juthomas/Electronics_MDMA/Images/MDMA_Images/8th_wonder.png

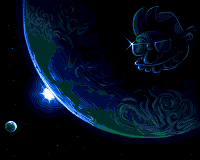
Images/MDMA_Images/8th_wonder.png
