juthomas/Electronics_MDMA/Images/MDMA_Images/background choice.png

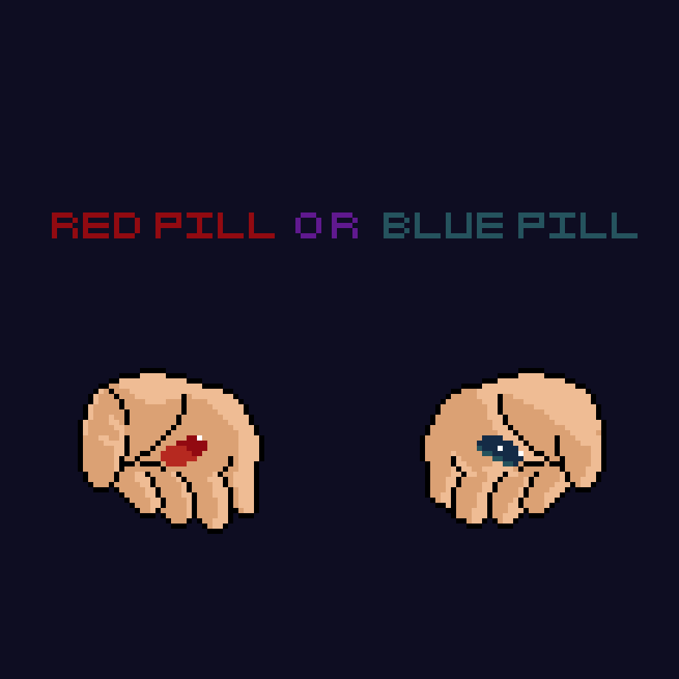
Images/MDMA_Images/background choice.png
