juthomas/Electronics_MDMA/Images/MDMA_Images/background hand.gif

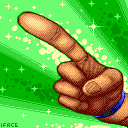
Images/MDMA_Images/background hand.gif
