juthomas/Electronics_MDMA/Images/MDMA_Images/background liar.gif

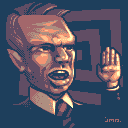
Images/MDMA_Images/background liar.gif
