juthomas/Electronics_MDMA/Images/MDMA_Images/background liar.png

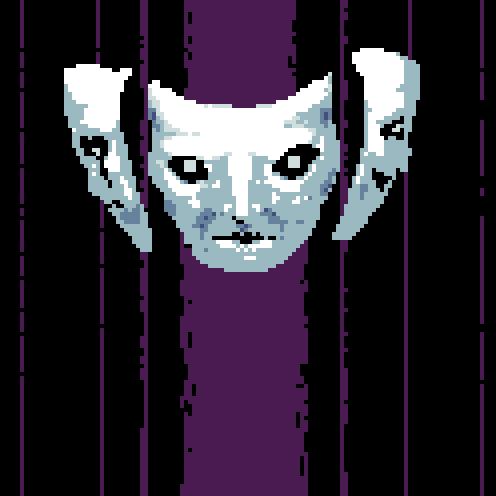
Images/MDMA_Images/background liar.png
