juthomas/Electronics_MDMA/Images/MDMA_Images/background roulette.jpeg

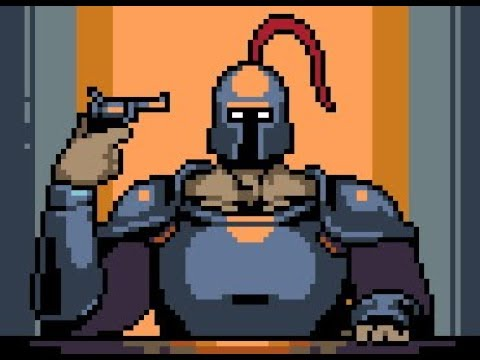
Images/MDMA_Images/background roulette.jpeg
