juthomas/Electronics_MDMA/Images/MDMA_Images/background_gunslayer.png

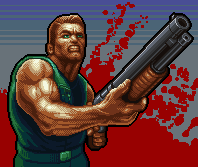
Images/MDMA_Images/background_gunslayer.png
