juthomas/Electronics_MDMA/Images/MDMA_Images/corridor.jpeg

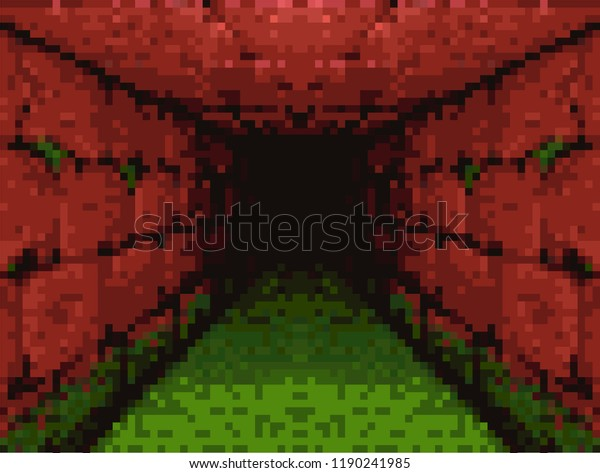
Images/MDMA_Images/corridor.jpeg
