juthomas/Electronics_MDMA/Images/MDMA_Images/Demonic.jpeg

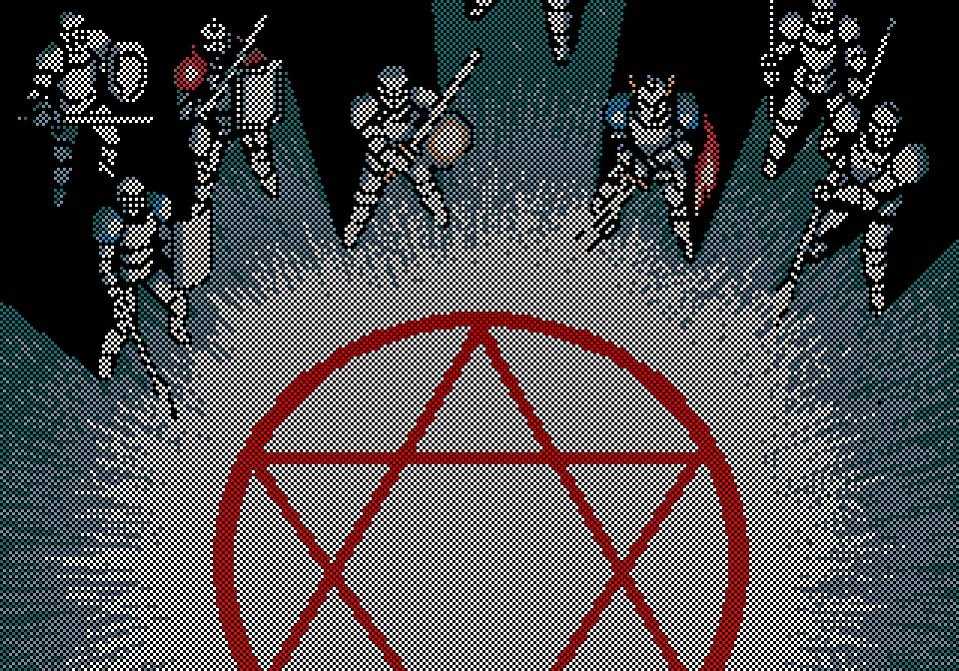
Images/MDMA_Images/Demonic.jpeg
