juthomas/Electronics_MDMA/Images/MDMA_Images/Drink.png

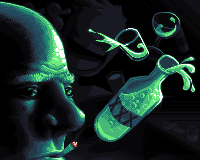
Images/MDMA_Images/Drink.png
