juthomas/Electronics_MDMA/Images/MDMA_Images/KingCrimson.png

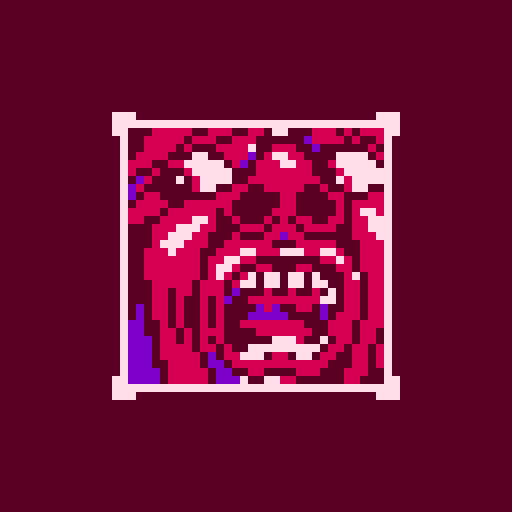
Images/MDMA_Images/KingCrimson.png
