juthomas/Electronics_MDMA/Images/MDMA_Images/time background.gif

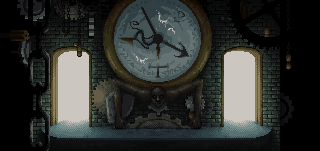
Images/MDMA_Images/time background.gif
