juthomas/Electronics_MDMA/Images/partition_megalovania.png

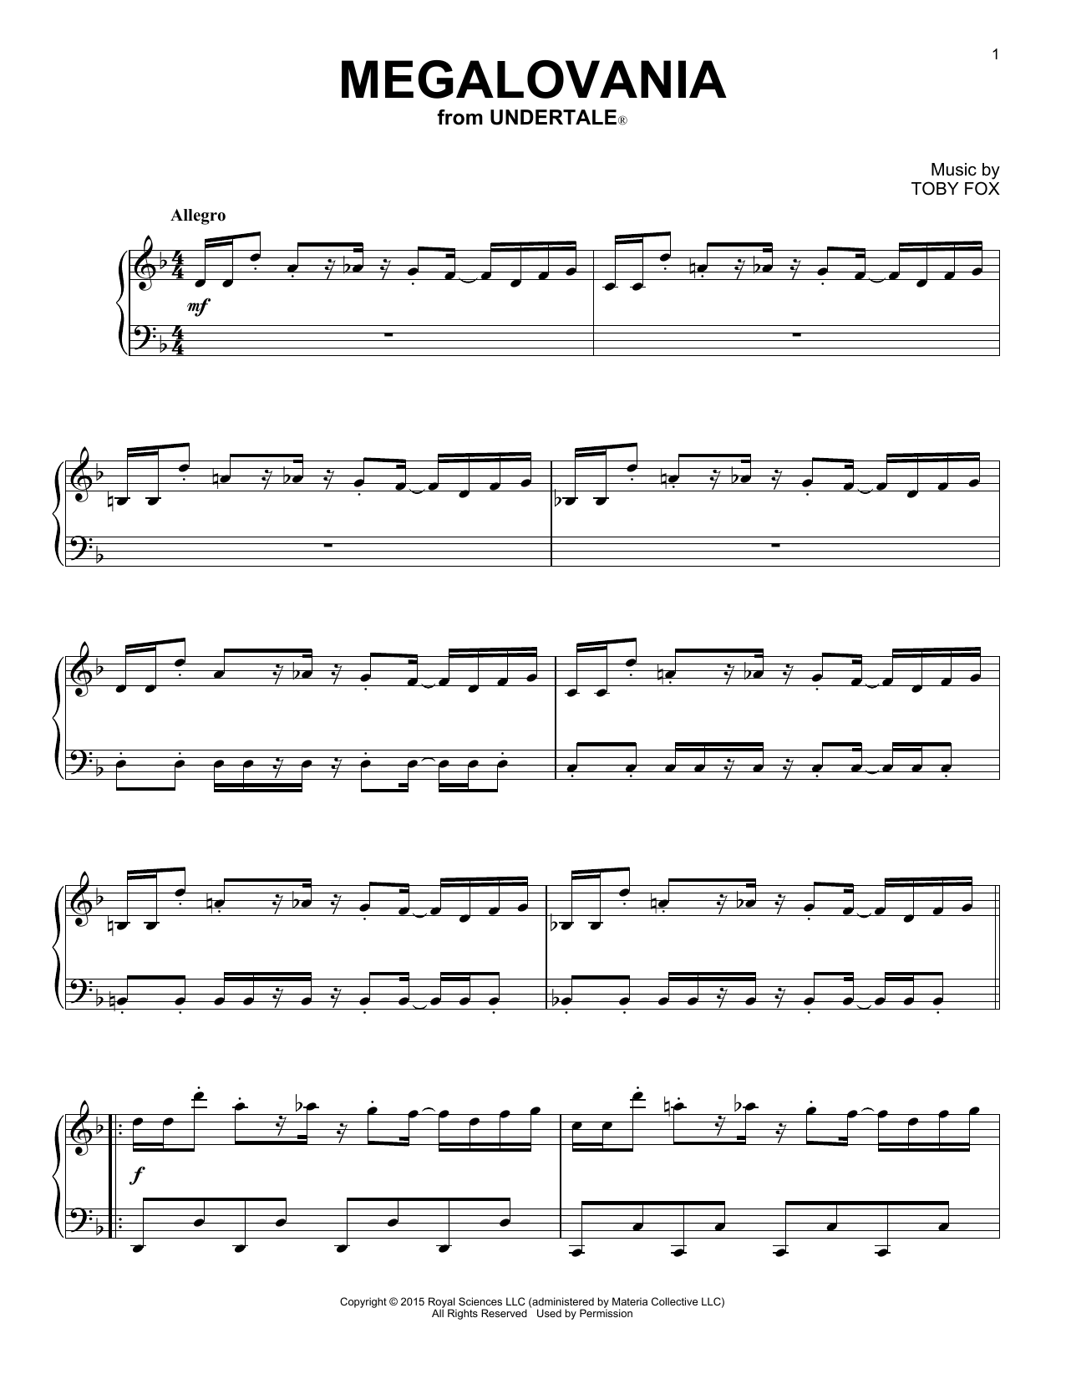
Images/partition_megalovania.png
