juthomas/Electronics_MDMA/MDMA_KICAD_V2/MDMA/MDMA.png

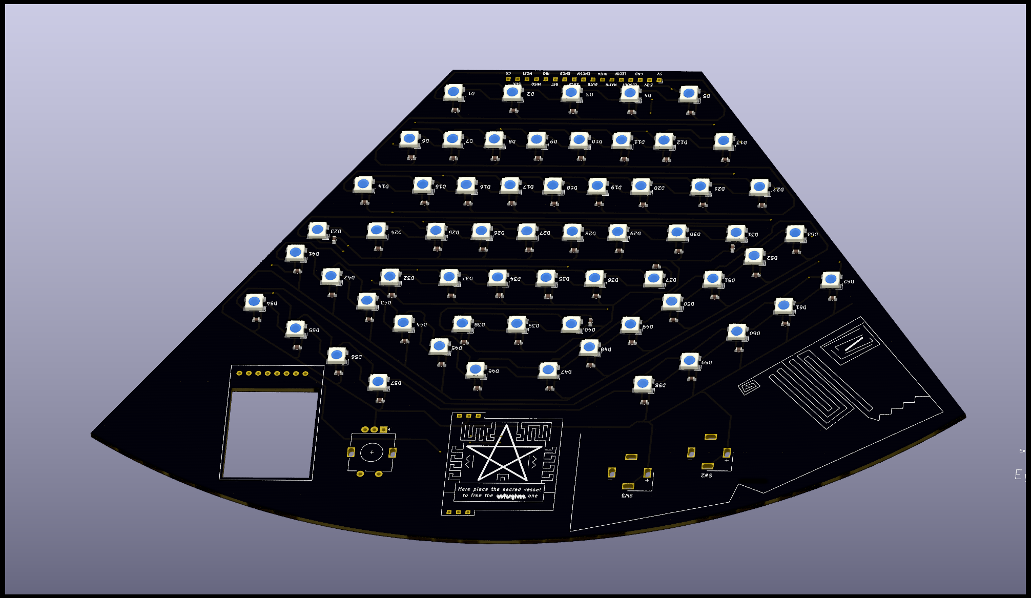
MDMA_KICAD_V2/MDMA/MDMA.png
