juthomas/Electronics_MDMA/Project/src/buttons/buttons.c

#include "../../inc/buttons.h"
# ifndef __AVR_ATmega2560__
#  define __AVR_ATmega2560__
#  define F_CPU 16000000
# endif
# include <avr/io.h>
# include <avr/interrupt.h>

#define FALSE 0
#define TRUE 1


static uint16_t order_counter = 1;

void	clear_buttons()
{
	order_counter = 1;
	for (uint8_t i = 0; i < 16; i++)
	{
		buttons_clicks_order[i] = 0;
	}
}

// uint16_t get_button_ticks(uint8_t index)
// {
// 	return ((buttons_clicks_order[index] & 0b1111111111100000) >> 5);
// }

// uint8_t get_button_order(uint8_t index)
// {
// 	return (buttons_clicks_order[index] & 0b1111);
// }

// uint8_t get_button_activation(uint8_t index)
// {
// 	return ((buttons_clicks_order[index] & 0b10000) >> 4);
// }

void init_buttons()
{
	clear_buttons();
	//Input Mode for respectively (from right to left)
	//Player 1 : A B
	//Player 2 : A B
	//Player 5 : A B
	//Player 4 : A B
	DDRC &= !(0b11111111);
	//Player 3 : A B
	DDRE &= !(0b00011000);
	//Encoders Clicks
	DDRE &= !(0b01110100);
	DDRG &= !(0b00100000);

	// noInterrupts
	cli();
	// Clear registers
	TCCR3A = 0;
	TCCR3B = 0;
	TCNT3 = 0;

	// 100 Hz (16000000/((624+1)*256))
	OCR3A = 624;
	// CTC
	TCCR3B |= (1 << WGM32);
	// Prescaler 256
	TCCR3B |= (1 << CS32);
	// Output Compare Match A Interrupt Enable
	TIMSK3 |= (1 << OCIE3A);
	// interrupts
	sei();
}



ISR(TIMER3_COMPA_vect)
{
	uint8_t is_button_clicked = FALSE;
	//Player 1 A
	if (PINC & (1 << 0))
	{
		if (!buttons_clicks_order[0])
		{
			buttons_clicks_order[0] &= 0b1111111111110000;
			buttons_clicks_order[0] |= order_counter & 0b1111;
			is_button_clicked = TRUE;
		}
		buttons_clicks_order[0] |= 0b0000000000010000;
		buttons_clicks_order[0] += 0b0000000000100000;
	}
	else
	{
		buttons_clicks_order[0] &= 0b1111111111101111;
	}
	//Player 1 B
	if (PINC & (1 << 1))
	{
		if (!buttons_clicks_order[1])
		{
			buttons_clicks_order[1] &= 0b1111111111110000;
			buttons_clicks_order[1] |= order_counter & 0b1111;
			is_button_clicked = TRUE;
		}
		buttons_clicks_order[1] |= 0b0000000000010000;
		buttons_clicks_order[1] += 0b0000000000100000;
	}
	else
	{
		buttons_clicks_order[1] &= 0b1111111111101111;
	}
	//Encoder 1
	if (PINE & (1 << 2))
	{
		if (!buttons_clicks_order[2])
		{
			buttons_clicks_order[2] &= 0b1111111111110000;
			buttons_clicks_order[2] |= order_counter & 0b1111;
			is_button_clicked = TRUE;
		}
		buttons_clicks_order[2] |= 0b0000000000010000;
		buttons_clicks_order[2] += 0b0000000000100000;
	}
	else
	{
		buttons_clicks_order[2] &= 0b1111111111101111;
	}
	//Player 2 A/
	if (PINC & (1 << 4))
	{
		if (!buttons_clicks_order[3])
		{
			buttons_clicks_order[3] &= 0b1111111111110000;
			buttons_clicks_order[3] |= order_counter & 0b1111;
			is_button_clicked = TRUE;
		}
		buttons_clicks_order[3] |= 0b0000000000010000;
		buttons_clicks_order[3] += 0b0000000000100000;
	}
	else
	{
		buttons_clicks_order[3] &= 0b1111111111101111;
	}
	//Player 2 B
	if (PINC & (1 << 5))
	{
		if (!buttons_clicks_order[4])
		{
			buttons_clicks_order[4] &= 0b1111111111110000;
			buttons_clicks_order[4] |= order_counter & 0b1111;
			is_button_clicked = TRUE;

		}
		buttons_clicks_order[4] |= 0b0000000000010000;
		buttons_clicks_order[4] += 0b0000000000100000;
	}
	else
	{
		buttons_clicks_order[4] &= 0b1111111111101111;
	}
	//Encoder 2
	if (PINE & (1 << 7))
	{
		if (!buttons_clicks_order[5])
		{
			buttons_clicks_order[5] &= 0b1111111111110000;
			buttons_clicks_order[5] |= order_counter & 0b1111;
			is_button_clicked = TRUE;
		}
		buttons_clicks_order[5] |= 0b0000000000010000;
		buttons_clicks_order[5] += 0b0000000000100000;
	}
	else
	{
		buttons_clicks_order[5] &= 0b1111111111101111;
	}
	//Player 3 A/
	if (PINC & (1 << 6))
	{
		if (!buttons_clicks_order[6])
		{
			buttons_clicks_order[6] &= 0b1111111111110000;
			buttons_clicks_order[6] |= order_counter & 0b1111;
			is_button_clicked = TRUE;
		}
		buttons_clicks_order[6] |= 0b0000000000010000;
		buttons_clicks_order[6] += 0b0000000000100000;
	}
	else
	{
		buttons_clicks_order[6] &= 0b1111111111101111;
	}
	//Player 3 B
	if (PINC & (1 << 7))
	{
		if (!buttons_clicks_order[7])
		{
			buttons_clicks_order[7] &= 0b1111111111110000;
			buttons_clicks_order[7] |= order_counter & 0b1111;
			is_button_clicked = TRUE;
		}
		buttons_clicks_order[7] |= 0b0000000000010000;
		buttons_clicks_order[7] += 0b0000000000100000;
	}
	else
	{
		buttons_clicks_order[7] &= 0b1111111111101111;
	}
	//Encoder 3
	if (PING & (1 << 5))
	{
		if (!buttons_clicks_order[8])
		{
			buttons_clicks_order[8] &= 0b1111111111110000;
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
	}
	else
	{
		buttons_clicks_order[15] &= 0b1111111111101111;
	}

	//Check if button is pressed and increment counter then
	if (is_button_clicked == TRUE)
	{
		if (order_counter < 15)
		{
			order_counter++;
		}
	}

	// digitalWrite(ledPin, digitalRead(ledPin) ^ 1);
}
