juthomas/Electronics_MDMA/Project/inc/background.h

const unsigned char DuelBG[] PROGMEM={0x00, 0x00, 0x00, 0x00, 0x00, 0x00, 0x00, 0x00, 0x00, 0x01, 0x12, 0x23, 0x00, 0x00, 0x00, 0x00, 0x11, 0x00, 0x00, 0x04, 0x33, 0x55, 0x43, 0x45, 0x55, 0x55, 0x55, 0x55, 0x55, 0x55, 0x55, 0x55, 0x55, 0x55, 0x55, 0x52, 0x33, 0x55, 0x55, 0x55, 
0x00, 0x00, 0x00, 0x00, 0x00, 0x00, 0x00, 0x00, 0x00, 0x20, 0x15, 0x30, 0x00, 0x00, 0x00, 0x01, 0x55, 0x00, 0x00, 0x55, 0x55, 0x40, 0x10, 0x15, 0x55, 0x55, 0x55, 0x55, 0x55, 0x55, 0x55, 0x55, 0x55, 0x55, 0x55, 0x50, 0x54, 0x45, 0x55, 0x55, 
0x00, 0x00, 0x00, 0x00, 0x00, 0x00, 0x00, 0x00, 0x00, 0x00, 0x00, 0x00, 0x00, 0x13, 0x31, 0x00, 0x00, 0x00, 0x35, 0x55, 0x55, 0x23, 0x16, 0x55, 0x55, 0x55, 0x55, 0x55, 0x55, 0x55, 0x55, 0x55, 0x55, 0x51, 0x33, 0x32, 0x25, 0x15, 0x55, 0x55, 
0x00, 0x00, 0x00, 0x00, 0x00, 0x00, 0x00, 0x00, 0x00, 0x00, 0x00, 0x00, 0x00, 0x05, 0x50, 0x00, 0x00, 0x05, 0x51, 0x05, 0x22, 0x25, 0x55, 0x55, 0x52, 0x55, 0x55, 0x55, 0x55, 0x55, 0x55, 0x55, 0x55, 0x36, 0x32, 0x42, 0x32, 0x35, 0x55, 0x55, 
0x00, 0x00, 0x00, 0x00, 0x00, 0x00, 0x00, 0x00, 0x00, 0x00, 0x00, 0x00, 0x00, 0x01, 0x00, 0x13, 0x30, 0x11, 0x15, 0x55, 0x00, 0x04, 0x55, 0x55, 0x50, 0x55, 0x55, 0x55, 0x55, 0x55, 0x55, 0x55, 0x51, 0x43, 0x25, 0x35, 0x64, 0x25, 0x55, 0x55, 
0x00, 0x00, 0x00, 0x00, 0x00, 0x00, 0x00, 0x00, 0x00, 0x00, 0x00, 0x00, 0x00, 0x54, 0x00, 0x30, 0x00, 0x00, 0x55, 0x55, 0x55, 0x55, 0x55, 0x55, 0x55, 0x55, 0x55, 0x55, 0x55, 0x55, 0x55, 0x55, 0x50, 0x52, 0x55, 0x45, 0x54, 0x25, 0x55, 0x55, 
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
0x05, 0x56, 0x10, 0x21, 0x11, 0x12, 0x21, 0x11, 0x11, 0x11, 0x12, 0x12, 0x01, 0x61, 0x54, 
};
const unsigned short CadreSquareBGPalette[] = {  0x7b4a, 0xb575, 0x9cd3, 0x9c6b, 0x5247, 0xd657, 0xef3c, 0x8be9, 0xaccd, 0x7307, 0x5224, 0x49a4, 0000, 0x632c, 0xa48a, };
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
