juthomas/Electronics_MDMA/Project/inc/intro.h

const unsigned char DevilEyesBG[] PROGMEM={0x00, 0x00, 0x00, 0x00, 0x00, 0x00, 0x00, 0x00, 0x00, 0x00, 0x00, 0x00, 0x00, 0x00, 0x00, 0x00, 
0x00, 0x00, 0x00, 0x00, 0x00, 0x00, 0x00, 0x00, 0x00, 0x00, 0x00, 0x00, 0x00, 0x00, 0x00, 0x00, 
0x00, 0x11, 0x11, 0x00, 0x00, 0x00, 0x00, 0x00, 0x00, 0x00, 0x00, 0x00, 0x00, 0x11, 0x11, 0x00, 
0x01, 0x22, 0x22, 0x11, 0x10, 0x00, 0x00, 0x00, 0x00, 0x00, 0x00, 0x01, 0x11, 0x22, 0x22, 0x10, 
0x01, 0x22, 0x22, 0x22, 0x21, 0x00, 0x00, 0x00, 0x00, 0x00, 0x00, 0x12, 0x22, 0x22, 0x22, 0x10, 
0x01, 0x22, 0x22, 0x00, 0x22, 0x11, 0x00, 0x00, 0x00, 0x00, 0x11, 0x22, 0x00, 0x22, 0x22, 0x10, 
0x01, 0x22, 0x20, 0x00, 0x02, 0x22, 0x10, 0x00, 0x00, 0x01, 0x22, 0x20, 0x00, 0x02, 0x22, 0x10, 
0x01, 0x22, 0x20, 0x00, 0x02, 0x22, 0x10, 0x00, 0x00, 0x01, 0x22, 0x20, 0x00, 0x02, 0x22, 0x10, 
0x01, 0x22, 0x20, 0x00, 0x02, 0x22, 0x21, 0x00, 0x00, 0x12, 0x22, 0x20, 0x00, 0x02, 0x22, 0x10, 
0x01, 0x22, 0x22, 0x00, 0x22, 0x22, 0x21, 0x00, 0x00, 0x12, 0x22, 0x22, 0x00, 0x22, 0x22, 0x10, 
0x00, 0x11, 0x12, 0x22, 0x22, 0x22, 0x21, 0x00, 0x00, 0x12, 0x22, 0x22, 0x22, 0x21, 0x11, 0x00, 
0x00, 0x00, 0x01, 0x11, 0x11, 0x11, 0x10, 0x00, 0x00, 0x01, 0x11, 0x11, 0x11, 0x10, 0x00, 0x00, 
};
const unsigned short DevilEyesBGPalette[] = {  0000, 0xffff, 0x9800, };

const unsigned char DevilSmileBG[] PROGMEM={0x00, 0x00, 0x00, 0x00, 0x00, 0x00, 0x00, 0x00, 0x00, 0x00, 0x00, 0x00, 0x00, 0x00, 0x00, 0x00, 
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
0x00, 0x00, 0x00, 0x00, 0x00, 0x00, 0x00, 0x00, 0x00, 0x00, 0x00, 0x00, 0x00, 0x00, 0x00, 0x00, 
};
const unsigned short BaphometBGPalette[] = {  0xffff, 0000, 0x39e7, 0x4248, 0x4208, 0x31a6, 0xb5b6, 0x4a49, 0x2965, 0xce99, 0xf7be, 0x1081, 0x5aeb, 0x2124, 0x6b6d, 0x7bef, };
