juthomas/Electronics_MDMA/Project/inc/matrix_progmem.h

#ifndef MATRIX_PROGMEM_H
# define MATRIX_PROGMEM_H
# include <stdint.h>

const uint8_t SWORD[] PROGMEM = "\0\0\0\0\0\0\0\0\0\0\0\0\0\0\0\1\1\1\15\15\15\20\21\20\0\0\0\0\0\0\0\0\0\0\0\0\1\1\1\15\15\15\20\21\20\10\11\12\0\1\0\0\1\0\0\0\0\1\1\1\15\15\15\20\21\20\10\11\12\0\0\1\13\21\0\13\21\0\1\2\1\15\15\15\20\21\20\10\11\12\0\0\1\0\0\0\1\2\0\13\21\1\15\15\15\20\21\20\10\11\12\0\0\1\0\0\0\0\0\0\0\1\0\5\14\3\13\21\1\10\11\12\1\1\1\0\0\0\0\0\0\0\0\0\5\13\3\5\13\3\3\11\5\13\21\0\13\21\0\0\1\0\0\0\0\0\0\0\2\10\5\2\10\5\0\0\0\1\2\0\13\21\0\0\1\0\0\0\0\0\0\0";
const uint8_t PURSE[] PROGMEM = "\0\0\0\0\0\0\7\16\3\7\16\4\7\16\4\2\11\5\1\1\1\0\0\0\0\0\0\0\0\0\0\1\0\13\21\0\13\21\0\2\3\0\0\0\0\0\0\0\0\0\0\0\0\0\13\21\0\7\16\3\7\16\4\3\11\5\0\1\0\0\0\0\2\3\0\7\16\3\13\21\0\7\16\3\7\16\4\7\16\4\2\11\5\0\1\0\7\16\3\7\16\4\7\16\4\13\21\0\7\16\3\7\16\4\2\11\5\2\10\5\7\16\3\7\16\4\7\16\4\7\16\4\7\16\4\3\11\5\2\10\5\2\10\5\7\16\4\7\16\4\7\16\4\7\16\4\3\11\5\2\10\5\2\10\5\2\10\5\0\2\0\2\10\5\2\10\5\2\10\5\2\10\5\2\10\5\2\10\5\0\1\0";
const uint8_t BOW[] PROGMEM = "\0\0\0\0\0\0\0\1\0\5\13\3\5\13\3\5\13\3\5\13\3\0\0\0\0\0\0\0\1\0\5\13\3\2\10\5\1\3\4\15\15\15\1\1\1\0\0\0\0\0\0\5\13\3\2\10\5\1\2\4\1\3\4\20\21\20\1\1\1\0\0\0\0\0\0\5\13\3\2\10\5\0\2\4\1\3\4\20\21\20\1\1\1\0\0\0\0\1\0\5\13\3\2\10\5\0\2\4\1\3\4\20\21\20\1\1\1\0\0\0\0\1\0\5\13\3\2\10\5\1\2\4\1\3\4\20\21\20\1\1\1\0\0\0\0\1\0\0\1\0\5\13\3\2\10\5\2\3\4\20\21\20\1\1\1\0\0\0\0\0\0\0\0\0\0\1\0\5\13\3\5\13\3\5\14\4\5\13\3\0\0\0";
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

#endif
