juthomas/Electronics_MDMA/Project/src/ili9341/dragon.h

#define DRAGON_WIDTH 110
#define DRAGON_HEIGHT 70

const PROGMEM uint16_t dragonBitmap[DRAGON_WIDTH * DRAGON_HEIGHT] = {
    0XFFFF, 0XFFFF, 0XFFFF, 0XFFFF, 0XFFFF, 0XFFFF, 0XFFFF, 0XFFFF, 0XFFFF,
    0XFFFF, 0XFFFF, 0XFFFF, 0XFFFF, 0XFFFF, 0XFFFF, 0XFFFF, 0XFFFF, 0XFFFF,
    0XFFFF, 0XFFFF, 0XFFFF, 0XFFFF, 0XFFFF, 0XFFFF, 0XFFFF, 0XFFFF, 0XFFFF,
    0XFFFF, 0XFFFF, 0XFFFF, 0XFFFF, 0XFFFF, 0XFFFF, 0XFFFF, 0XFFFF, 0XFFFF,
    0XFFFF, 0XFFFF, 0XFFFF, 0XFFFF, 0XFFFF, 0XFFFF, 0XFFFF, 0XFFFF, 0XFFFF,
    0XFFFF, 0XFFFF, 0XFFFF, 0XFFFF, 0XFFFF, 0XFFFF, 0XFFFF, 0XFFFF, 0XFFFF,
    0XFFFF, 0XFFFF, 0XFFFF, 0XFFFF, 0XFFFF, 0XFFFF, 0XFFFF, 0XFFFF, 0XFFFF,
    0XFFFF, 0XFFFF, 0XFFFF, 0XFFFF, 0XFFFF, 0XFFFF, 0XFFFF, 0XFFFF, 0XFFFF,
    0XFFFF, 0XFFFF, 0XFFFF, 0XFFFF, 0XFFFF, 0XFFFF, 0XFFFF, 0XFFFF, 0XFFFF,
    0XFFFF, 0XFFFF, 0XFFFF, 0XFFFF, 0XFFFF, 0XFFFF, 0XFFFF, 0XFFFF, 0XFFFF,
    0XFFFF, 0XFFFF, 0XFFFF, 0XFFFF, 0XFFFF, 0XFFFF, 0XFFFF, 0XFFFF, 0XFFFF,
    0XFFFF, 0XFFFF, 0XFFFF, 0XFFFF, 0XFFFF, 0XFFFF, 0XFFFF, 0XFFFF, 0XFFFF,
    0XFFFF, 0XFFFF, 0XFFFF, 0XFFFF, 0XFFFF, 0XFFFF, 0XFFFF, 0XFFFF, 0XFFFF,
    0XFFFF, 0XFFFF, 0XFFFF, 0XFFFF, 0XFFFF, 0XFFFF, 0XFFFF, 0XFFFF, 0XFFFF,
    0XFFFF, 0XFFFF, 0XFFFF, 0XFFFF, 0XFFFF, 0XFFFF, 0XFFFF, 0XFFFF, 0XFFFF,
    0XFFFF, 0XFFFF, 0XFFFF, 0XFFFF, 0XFFFF, 0XFFFF, 0XFFFF, 0XFFFF, 0XFFFF,
    0XFFFF, 0XFFFF, 0XFFFF, 0XFFFF, 0XFFFF, 0XFFFF, 0XFFFF, 0XFFFF, 0XFFFF,
    0XFFFF, 0XFFFF, 0XFFFF, 0XFFFF, 0XFFFF, 0XFFFF, 0XFFFF, 0XFFFF, 0XFFFF,
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
    0X0547, 0X0547, 0X0547, 0X0547, 0X0547, 0X0547, 0X0547, 0X0547, 0X0547,
    0X0547, 0X0547, 0X0547, 0X0547, 0X0547, 0X0547, 0X0547, 0X0547, 0X0547,
    0X0547, 0X0547, 0X0547, 0X0547, 0X0547, 0X0547, 0X0547, 0X0547, 0X0547,
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
    };
